pedroren/pekeboard/pekepad-v/cases/top_gasket.stl

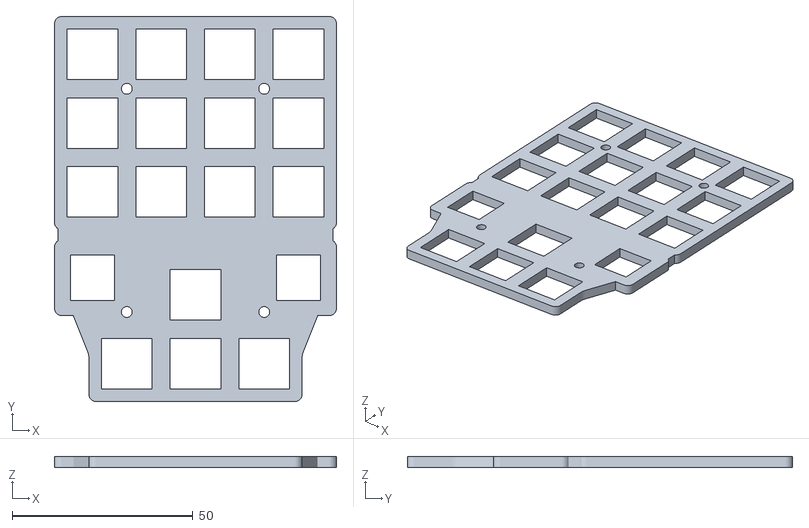
[picture p19: CAD file, 2026-07-04]
pekepad-v/cases/top_gasket.stl
78.0 x 106.5 x 3.00
