pedroren/pekeboard/kicad/3dmodels/SW_SPDT_PCM12.step

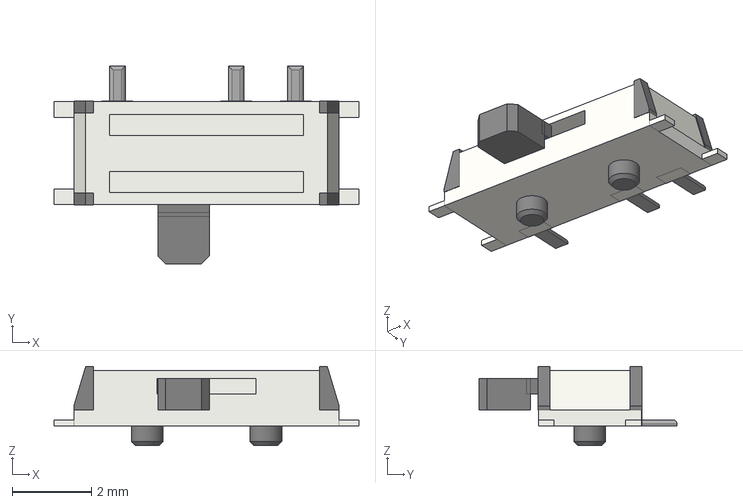
[picture p20: CAD file, 2026-03-06]
kicad/3dmodels/SW_SPDT_PCM12.step
7.70 x 5.00 x 2.00 mm
