pedroren/pekeboard/pekeboard/cases/top_gasket.stl

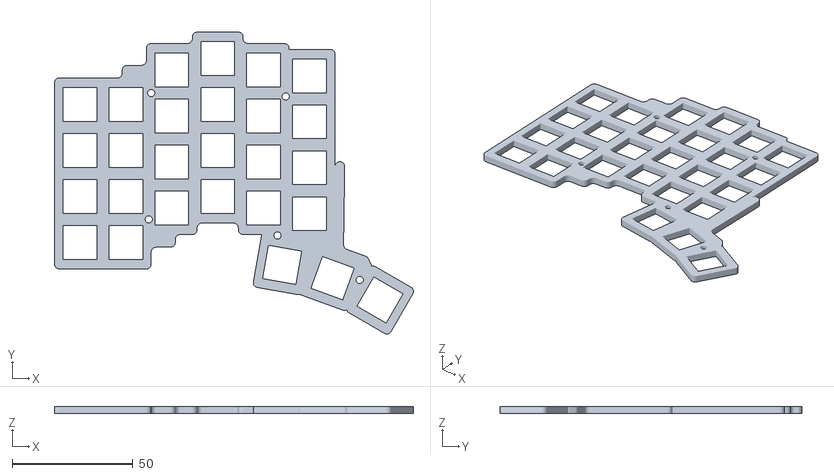
[picture p21: CAD file, 2026-06-26]
pekeboard/cases/top_gasket.stl
148.5 x 124.9 x 3.00
