pedroren/pekeboard/pekepad-v/cases/pcb.stl

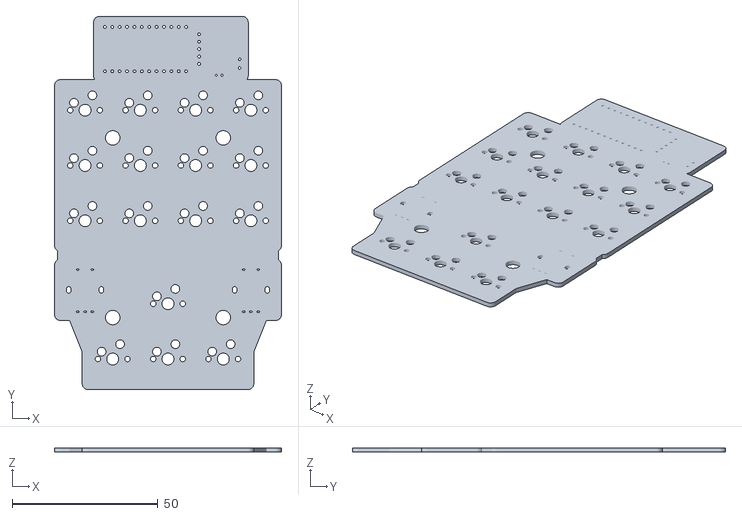
[picture p22: CAD file, 2026-04-15]
pekepad-v/cases/pcb.stl
78.0 x 128.2 x 1.51
