pedroren/pekeboard/pekepad/cases/pekepad_pcb.stl

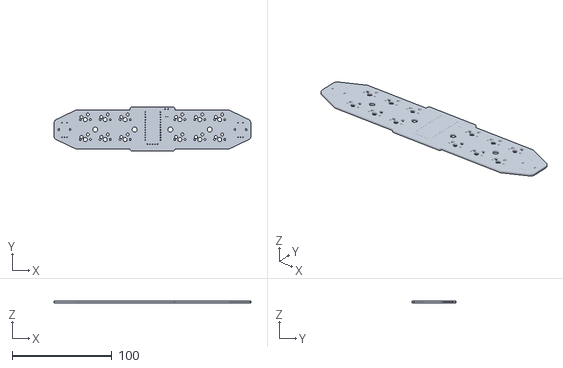
[picture p23: CAD file, 2026-03-21]
pekepad/cases/pekepad_pcb.stl
197.7 x 43.9 x 1.51
