pedroren/pekeboard/kicad/3dmodels/JST_PH_S2B-PH-K_1x02_P2.00mm_Horizontal.step

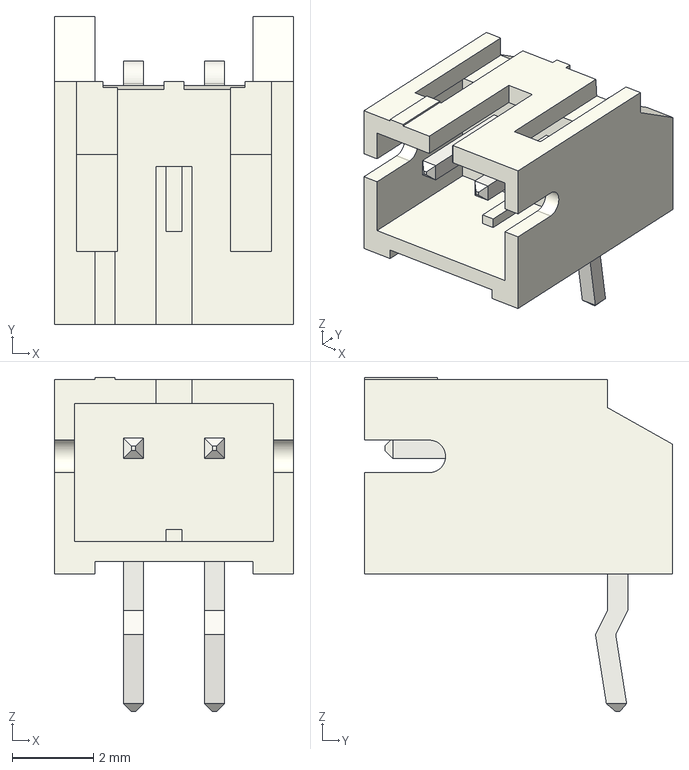
[picture p24: CAD file, 2026-03-06]
kicad/3dmodels/JST_PH_S2B-PH-K_1x02_P2.00mm_Horizontal.step
5.90 x 7.60 x 8.25 mm
