pedroren/pekeboard/pekeboard/cases/switch_plate.stl

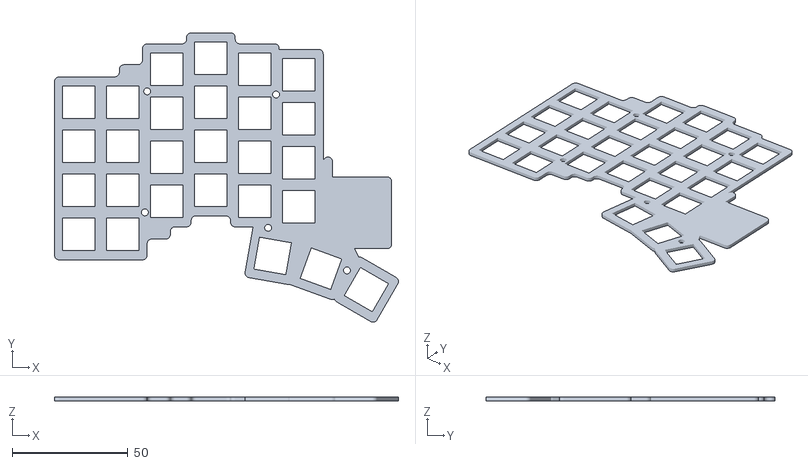
[picture p25: CAD file, 2026-06-26]
pekeboard/cases/switch_plate.stl
148.5 x 124.9 x 1.60
