pedroren/pekeboard/pekepad-v/cases/switch_plate.stl

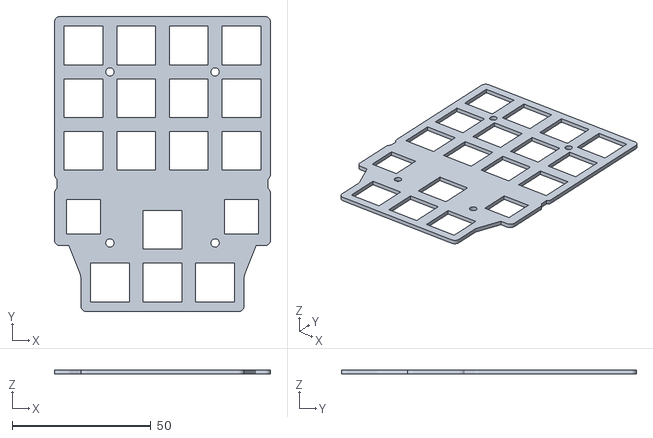
[picture p26: CAD file, 2026-04-15]
pekepad-v/cases/switch_plate.stl
78.0 x 106.5 x 1.60
