pedroren/pekeboard/kicad/3dmodels/D_SOD-123.step

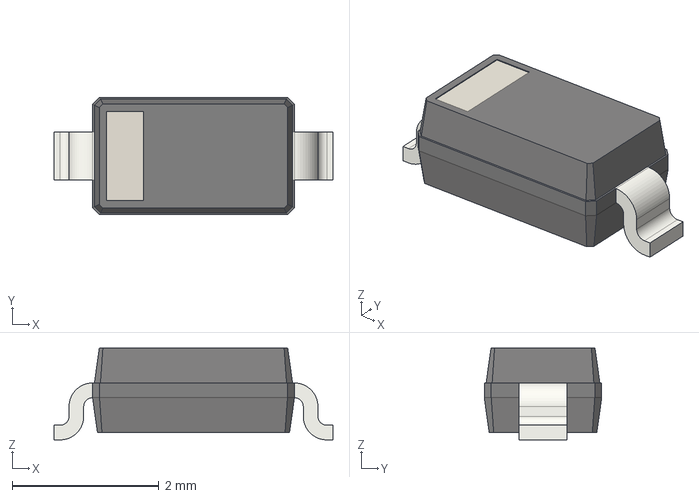
[picture p27: CAD file, 2026-03-06]
kicad/3dmodels/D_SOD-123.step
3.80 x 1.60 x 1.25 mm
