pedroren/pekeboard/pekeboard/cases/pcb_l.stl

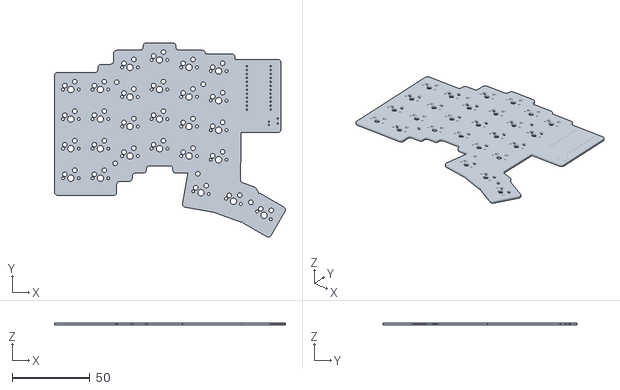
[picture p28: CAD file, 2026-06-18]
pekeboard/cases/pcb_l.stl
148.5 x 124.9 x 1.51
