pedroren/pekeboard/pekeboard/cases/plate_support.stl

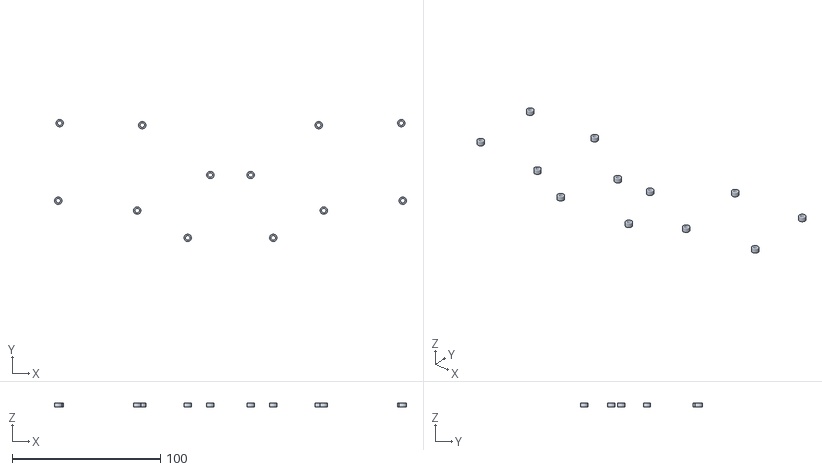
[picture p29: CAD file, 2026-06-07]
pekeboard/cases/plate_support.stl
237.1 x 82.3 x 3.00
