pedroren/pekeboard/pekeboard/cases/pcb.stl

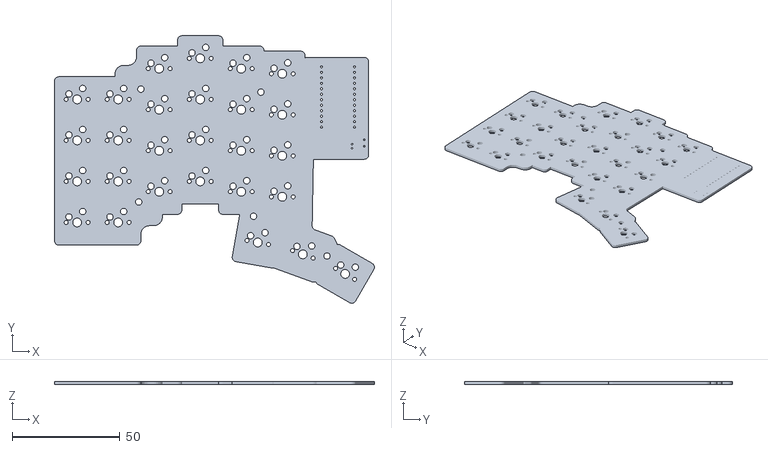
[picture p30: CAD file, 2026-06-07]
pekeboard/cases/pcb.stl
148.2 x 123.9 x 1.51
