pedroren/pekeboard/pekeboard/config.yaml

meta:
  name: pepekey
  version: 1.0
  engine: 4.1.0
  author: pedroren
units:
  kx: u
  ky: u
  p: 0
  # padding for outer keys
  px: 2
  kpx: kx+px
  py: 3
  kpy: ky+py
  # components size
  mcu_y: 34.1
  mcu_x: 18.3
  mcu_d: 3.3+12 # mcu+sockets
  batt_x: 18
  batt_y: 32
  batt_d: 6.5 
  # Defaults to M2 Screws
  screw_size: 1.5
  standoff_size: 2.5
  # Case
  case_d: 1.5
  pcb_d: 1.6
  plate_pcb_gap: 3
  bottom_pcb_gap: 2
  usb_access_x: 13
  usb_access_d: 6
  case_y: case_d+bottom_pcb_gap+pcb_d+plate_pcb_gap+pcb_d
points:
  zones:
    matrix:
      anchor:
        shift: [100, -120] #kicad
      key:
        padding: ky+p
        spread: kx+p
        tags: mx_key
      columns:
        outer:
          key:
            column_net: P008
        pinky:
          key:
            column_net: P022
        ring:
          key:
            stagger: 3u/4
            column_net: P024
        middle:
          key:
            stagger: 1u/4
            column_net: P100
        index:
          key:
            stagger: -1u/4
            column_net: P011
        inner:
          key:
            stagger: -1u/8
            column_net: P106
      rows:
        bottom:
          row_net: P031
        home:
          row_net: P029
        top:
          row_net: P002
        num:
          row_net: P115
    thumbs:
      key:
        padding: ky
        spread: kx+1
        tags: mx_key
      anchor:
        ref:  matrix_inner_bottom
        shift:  [-1u/2,  -1u]
      columns:
        outer:
          key:
            splay: -10
            origin: [-0.7 u, +0.5 u]
            column_net: P011
        middle:
          key:
            splay: -10
            #stagger: -1u/6
            origin: [-0.5 u, -0.5 u]
            #rotate: -6
            column_net: P106
        inner:
          key:
            splay: -10
            #stagger: -1u/4
            #rotate: -6
            origin: [-0.5 u, -0.5 u]
            column_net: P111
      rows:
        thumbrow:
          row_net: P113
    mount_top_left:
      key.tags: [mount]
      anchor:
        - ref: matrix_ring_top
          shift: [-0.5kx +1, 0.5 ky]
    mount_bottom_left:
      key.tags: [mount]
      anchor:
        - ref: matrix_ring_bottom
          shift: [-0.5kx, -0.25ky]
    mount_top_right:
      key.tags: [mount]
      anchor:
        - ref: matrix_inner_top
          shift: [-0.52 kx, .5ky+1]
    mount_palm:
      key.tags: [mount]
      anchor:
        - ref: matrix_index_bottom
          shift: [.3kx, -.6ky]
    mount_thumb:
      key.tags: [mount]
      anchor:
        - ref: thumbs_inner_thumbrow
          shift: [-0.6 kx, 3]
    controller:
      key.tags: [mcu]          
      anchor: 
        - ref: matrix_inner_top
          shift: [.5kx+mcu_x-2, .5ky]
          rotate: 0
    reset_button:
      key.tags: [reset_btn]          
      anchor: 
        - ref: controller
          shift: [.5mcu_x+3, 2]
    power_button:
      key.tags: [power_btn]          
      anchor: 
        - ref: controller
          shift: [.5mcu_x+3, -.75mcu_y+3]          
    case_mount_battery:          
      key.tags: [case_mount]
      anchor:
        - ref: power_button
          shift: [-2, -10]
  mirror:  &mirror
    ref: controller
    distance: 2.5kx        
outlines:
  raw:
    - what: rectangle
      where: [mx_key]
      size: [kx, ky]
      corner: px
    - what: rectangle
      where: [mcu]
      size: [mcu_x, mcu_y]
      corner: px        
    - what: rectangle
      where: [-mx_key,-mcu]
      size: [kx/2, ky/2]
      corner: px      
  keycaps:
    - what: rectangle 
      where: [mx_key]
      size: [kx, ky] 
      corner: 1
  switches:
    - what: rectangle
      where: [mx_key]
      size: 14
  controller:
    - what: rectangle
      where: [mcu]
      size: [mcu_x, mcu_y]
  usb_access:      
    - what: rectangle
      where: [mcu]
      size: [usb_access_x, usb_access_d]
      adjust.shift: [0, .5mcu_y+3]
      corner: 2
  reset_access:
    - what: circle
      where: reset_button
      radius: 2
      adjust.shift: [1.5, 0]
  power_access:      
    - what: rectangle
      where: power_button
      size: [pcb_d+1, usb_access_x-2]
      adjust.shift: [case_d, 0]    
  controller_area:
    - what: rectangle
      where: [mcu]        
      size: [1.5mcu_x+3, 1.5mcu_y-4]
      corner: px
      adjust.shift: [-1,-.25mcu_y+2]
  controller_cover:
     - what: outline
       name: controller_area
       operation: add
     - what: rectangle      
       size: [1.5mcu_x+3, 10]
       corner: px
       where: [mcu]        
       adjust.shift: [-1, -mcu_y]
  battery_area: #Batt/Cable cover
    - what: rectangle
      where: [mcu]
      size: [1.5mcu_x+5, batt_y-1] 
      adjust.shift: [-2, -.5mcu_y-.5batt_y-17]
      corner: px
    - what: rectangle  #Remove right side
      where: mirror_controller            
      size: [200, 200]        
      adjust:
        shift: [-80, 0]
      operation: subtract    
  screw_holes:
    - what: circle
      radius: screw_size    
      where: [mount, case_mount]
  mounting_holes:
    - what: circle
      radius: standoff_size    
      where: [mount, case_mount]
  mounting_holes_left:
    - what: circle
      radius: standoff_size    
      where: [mount, case_mount]    
    - what: rectangle  #Remove right side
      where: mirror_controller            
      size: [200, 200]        
      adjust:
        shift: [-80, 0]
      operation: subtract  
  pcb_support:
    - what: outline
      name: screw_holes
      expand: 1
    - what: rectangle  #Remove right side
      where: mirror_controller            
      size: [200, 200]        
      adjust:
        shift: [-80, 0]
      operation: subtract    
  keywell:
    - what: rectangle 
      where: [mx_key]
      size: [kpx, kpy] 
      corner: 2
      fillet: 2
      bound: true
  thumbs_patch:
    - what: polygon
      operation: stack
      fillet: 2
      points:
        - ref:  thumbs_outer_thumbrow
          shift: [-0.5kpx, -0.5kpy]
        - ref:  thumbs_middle_thumbrow
          shift: [-0.5kpx, -0.5kpy]
        - ref:  thumbs_inner_thumbrow
          shift: [-0.5kpx, -0.5kpy]
        - ref:  thumbs_inner_thumbrow
          shift: [0kpx, 0kpy]          
        - ref:  thumbs_inner_thumbrow
          shift: [-0.5kpx, 0.5kpy]
        - ref:  thumbs_middle_thumbrow
          shift: [0.5kpx, 0.6kpy]
        - ref:  thumbs_middle_thumbrow
          shift: [0kpx, 0.6kpy]
        - ref:  matrix_inner_home # Easier routing
          shift: [.70kpx, 0.6kpy]
        - ref:  thumbs_outer_thumbrow
          shift: [0.5kpx, 0.85kpy]          
        - ref:  thumbs_outer_thumbrow
          shift: [-0.5kpx, 0.75kpy]          
  thumbs_patch_r:
    - what: polygon
      operation: stack
      fillet: 2
      points:
        - ref:  mirror_thumbs_outer_thumbrow
          shift: [-0.5kpx, -0.5kpy]
        - ref:  mirror_thumbs_middle_thumbrow
          shift: [-0.5kpx, -0.5kpy]
        - ref:  mirror_thumbs_inner_thumbrow
          shift: [-0.5kpx, -0.5kpy]
        - ref:  mirror_thumbs_inner_thumbrow
          shift: [0kpx, 0kpy]          
        - ref:  mirror_thumbs_inner_thumbrow
          shift: [-0.5kpx, 0.5kpy]
        - ref:  mirror_thumbs_middle_thumbrow
          shift: [0.5kpx, 0.6kpy]
        - ref: mirror_thumbs_middle_thumbrow
          shift: [0kpx, 0.6kpy]
        - ref: mirror_matrix_inner_home # Easier routing
          shift: [.70kpx, 0.6kpy]
        - ref:  mirror_thumbs_outer_thumbrow
          shift: [0.5kpx, 0.85kpy]          
        - ref:  mirror_thumbs_outer_thumbrow
          shift: [-0.5kpx, 0.75kpy]                    
  base_outline:
    - keywell
    - name: thumbs_patch
      operation: add
      joints: beveled
      fillet: 2
      bound: true
    - name: thumbs_patch_r
      operation: add
      joints: beveled
      fillet: 2
      bound: true
    - controller_area
  bottom_outline:
    - base_outline
    - name: battery_area
      operation: add
      joints: beveled
      fillet: 2
    - -screw_holes
    - what: rectangle  #Remove right side
      where: mirror_controller            
      size: [200, 200]        
      adjust:
        shift: [-80, 0]
      operation: subtract
  outer_area:
    - what: outline
      name: bottom_outline
      expand: case_d+1
      joints: beveled
    - what: rectangle  #Remove right side
      where: mirror_controller            
      size: [200, 200]        
      adjust:
        shift: [-80, 0]
      operation: subtract
  plate:
    - keywell
    - thumbs_patch
    - thumbs_patch_r
    - "-switches"
    - "-screw_holes"
    - what: rectangle  #Remove right side
      where: mirror_controller            
      size: [200, 200]        
      adjust:
        shift: [-80, 0]
      operation: subtract
  pcb:
    - base_outline
    - "-screw_holes"     
  pcb_left:
    - what: outline
      name: pcb
      operation: add        
    - what: rectangle  #Remove right side
      where: mirror_controller            
      size: [200, 200]        
      adjust:
        shift: [-80, 0]
      operation: subtract
  pcb_right:
    - what: outline
      name: pcb
    - what: rectangle #Remove left side
      where: '/^controller/'
      size: [200, 200]        
      adjust:
        shift: [-80, 0]
      operation: subtract
  # For verification
  switches_screws: 
    - base_outline
    - -switches
    - -mounting_holes
  pcb_switches: 
    - pcb
    - -switches
  pcb_keycaps: 
    - pcb
    - -keycaps
pcbs:
  top_plate:
    template: kicad8
    outlines:
      edge:
        outline: plate
        layer: Edge.Cuts
  bottom_plate:
    template: kicad8
    outlines:
      edge:
        outline: bottom_outline
        layer: Edge.Cuts        
  pepekey_l:
    template: kicad8
    outlines:
      main:
        outline: pcb_left
        layer: Edge.Cuts
        asym: source 
    footprints:
      # gnd_fillzone:
      #   what: ceoloide/utility_filled_zone
      #   where:
      #     ref.aggregate.parts: [matrix_outer_top]
      mounting_holes:
        what: ceoloide/mounting_hole_npth
        where:  '/^mount_/'
      mx_hotswap:
        what: ceoloide/switch_mx
        where: '/^(matrix|thumbs)_/'
          #- /matrix_.*/
          #- /thumbs_.*/          
        params:
          include_keycap: true
          reversible: false
          hotswap: true
          from: "{{column_net}}"
          to: "{{colrow}}"
          switch_3dmodel_filename: '${KIPRJMOD}/../../kicad/3dmodels/SW_Hotswap_Kailh_MX.stp'
          switch_3dmodel_xyz_rotation: [0,180,180]
          switch_3dmodel_xyz_offset: [0, 0, -1.9]
      diode:
        what: ceoloide/diode_tht_sod123
        where: '/^(matrix|thumbs)_/'
          #- /matrix_.*/
          #- /thumbs_.*/
        adjust.shift: [0, -5]
        params:
          reversible: false
          side: B
          from: "{{colrow}}"
          to: "{{row_net}}"
          diode_3dmodel_filename: '${KIPRJMOD}/../../kicad/3dmodels/D_SOD-123.step'
      mcu:
        what: ceoloide/mcu_nice_nano
        where: '/^controller/'#mcu
        params:
          #side: F
          reversible: false
          show_via_labels: false
          P21_label: "031"
          P20_label: "029"
          P19_label: "002"
          P18_label: "115"
          P15_label: "113"
          P14_label: "111"
          P16_label: "010"
          P10_label: "009"
          P1_label: "006"
          P0_label: "008"
          P2_label: "017"
          P3_label: "020"
          P4_label: "022"
          P5_label: "024"
          P6_label: "100"
          P7_label: "011"
          P8_label: "104"
          P9_label: "106"
          P21: P031
          P20: P029
          P19: P002
          P18: P115
          P15: P113
          P14: P111
          P16: P010
          P10: P009
          P1: P006
          P0: P008
          P2: P017
          P3: P020
          P4: P022
          P5: P024
          P6: P100
          P7: P011
          P8: P104
          P9: P106
      reset_switch:
        what: ceoloide/reset_switch_smd_side
        where: '/^reset_button/'#[reset_btn]
        adjust:
          shift: [0, 0]
          rotate: 270
        params:
          reversible: false          
          from: GND
          to: RST
          reset_switch_3dmodel_filename: '${KIPRJMOD}/../../kicad/3dmodels/Panasonic_EVQPUJ_EVQPUA.step'
          reset_switch_3dmodel_xyz_rotation: [0,0,0]
      power_switch:
        what: ceoloide/power_switch_smd_side
        params:
          reversible: false
          side: F
          switch_3dmodel_filename: '${KIPRJMOD}/../../kicad/3dmodels/SW_SPDT_PCM12.step'
          switch_3dmodel_xyz_rotation: [0,0,-90]
        where:  '/^power_button/'#[power_btn]
        adjust:
          shift: [0, 0]
          rotate: 0
      batt_connector:
        what: ceoloide/battery_connector_jst_ph_2
        params:
          reversible: false
          side: F
          battery_connector_3dmodel_filename: '${KIPRJMOD}/../../kicad/3dmodels/JST_PH_S2B-PH-K_1x02_P2.00mm_Horizontal.step'
          battery_connector_3dmodel_xyz_rotation: [0,0,0]
          battery_connector_3dmodel_xyz_offset: [-1, 0, 0]
        where:  '/^controller/'#[mcu]
        adjust:
          shift: [.5kx-3, -.5mcu_y-7]
          rotate: -90
      pcb_label:
        what: ceoloide/utility_text
        params:
          text: 'Pekeboard v1.0 by pedroren'    
        where:  '/^matrix_inner_bottom/'
        adjust:
          shift: [1/2kx+2,0]
          rotate: -90    
  pepekey_r:
    template: kicad8
    outlines:
      main:
        outline: pcb_right
        layer: Edge.Cuts
        asym: source 
    footprints:
      # gnd_fillzone:
      #   what: ceoloide/utility_filled_zone
      #   where:
      #     ref.aggregate.parts: [matrix_outer_top]
      mounting_holes:
        what: ceoloide/mounting_hole_npth
        where:  '/^mirror_mount_/'
      mx_hotswap:
        what: ceoloide/switch_mx
        where: '/^(mirror_matrix|mirror_thumbs)_/'
          #- /matrix_.*/
          #- /thumbs_.*/          
        params:
          include_keycap: true
          reversible: false
          hotswap: true
          from: "{{column_net}}"
          to: "{{colrow}}"
          switch_3dmodel_filename: '${KIPRJMOD}/../../kicad/3dmodels/SW_Hotswap_Kailh_MX.stp'
          switch_3dmodel_xyz_rotation: [0,180,180]
          switch_3dmodel_xyz_offset: [0, 0, -1.9]
      diode:
        what: ceoloide/diode_tht_sod123
        where: '/^(mirror_matrix|mirror_thumbs)_/'
          #- /matrix_.*/
          #- /thumbs_.*/
        adjust.shift: [0, -5]
        params:
          reversible: false
          side: B
          from: "{{colrow}}"
          to: "{{row_net}}"
          diode_3dmodel_filename: '${KIPRJMOD}/../../kicad/3dmodels/D_SOD-123.step'
      mcu:
        what: ceoloide/mcu_nice_nano
        where: '/^mirror_controller/'#mcu
        params:
          #side: F
          reversible: false
          show_via_labels: false
          P21_label: "031"
          P20_label: "029"
          P19_label: "002"
          P18_label: "115"
          P15_label: "113"
          P14_label: "111"
          P16_label: "010"
          P10_label: "009"
          P1_label: "006"
          P0_label: "008"
          P2_label: "017"
          P3_label: "020"
          P4_label: "022"
          P5_label: "024"
          P6_label: "100"
          P7_label: "011"
          P8_label: "104"
          P9_label: "106"
          P21: P031
          P20: P029
          P19: P002
          P18: P115
          P15: P113
          P14: P111
          P16: P010
          P10: P009
          P1: P006
          P0: P008
          P2: P017
          P3: P020
          P4: P022
          P5: P024
          P6: P100
          P7: P011
          P8: P104
          P9: P106
      reset_switch:
        what: ceoloide/reset_switch_smd_side
        where: '/^mirror_reset_button/'#[reset_btn]
        adjust:
          shift: [0, 0]
          rotate: 270
        params:
          reversible: false          
          from: GND
          to: RST
          reset_switch_3dmodel_filename: '${KIPRJMOD}/../../kicad/3dmodels/Panasonic_EVQPUJ_EVQPUA.step'
          reset_switch_3dmodel_xyz_rotation: [0,0,0]
      power_switch:
        what: ceoloide/power_switch_smd_side
        params:
          reversible: false
          side: F
          switch_3dmodel_filename: '${KIPRJMOD}/../../kicad/3dmodels/SW_SPDT_PCM12.step'
          switch_3dmodel_xyz_rotation: [0,0,-90]
        where:  '/^mirror_power_button/'#[power_btn]
        adjust:
          shift: [0, 0]
          rotate: 180
      batt_connector:
        what: ceoloide/battery_connector_jst_ph_2
        params:
          reversible: false
          side: F
          battery_connector_3dmodel_filename: '${KIPRJMOD}/../../kicad/3dmodels/JST_PH_S2B-PH-K_1x02_P2.00mm_Horizontal.step'
          battery_connector_3dmodel_xyz_rotation: [0,0,0]
          battery_connector_3dmodel_xyz_offset: [-1, 0, 0]
        where:  '/^mirror_controller/'#[mcu]
        adjust:
          shift: [.5kx-3, -.5mcu_y-7]
          rotate: -90        
      pcb_label:
        what: ceoloide/utility_text
        params:
          text: 'Pekeboard v1.0 by pedroren'    
        where:  '/^mirror_matrix_inner_bottom/'
        adjust:
          shift: [1/2kx+2,0]
          rotate: -90
  pepekey_dual: #reversible version
    template: kicad8
    outlines:
      main:
        outline: pcb_left
        layer: Edge.Cuts
        asym: source 
    footprints:
      # gnd_fillzone:
      #   what: ceoloide/utility_filled_zone
      #   where:
      #     ref.aggregate.parts: [matrix_outer_top]
      mounting_holes:
        what: ceoloide/mounting_hole_npth
        where:  '/^mount_/'
      mx_hotswap:
        what: ceoloide/switch_mx
        where: '/^(matrix|thumbs)_/'
          #- /matrix_.*/
          #- /thumbs_.*/          
        params:
          include_keycap: true
          reversible: true
          hotswap: true
          from: "{{column_net}}"
          to: "{{colrow}}"
          switch_3dmodel_filename: '${KIPRJMOD}/../../kicad/3dmodels/SW_Hotswap_Kailh_MX.stp'
          switch_3dmodel_xyz_rotation: [0,180,180]
          switch_3dmodel_xyz_offset: [0, 0, -1.9]
      diode:
        what: ceoloide/diode_tht_sod123
        where: '/^(matrix|thumbs)_/'
          #- /matrix_.*/
          #- /thumbs_.*/
        adjust.shift: [0, -5]
        params:
          reversible: true
          side: B
          from: "{{colrow}}"
          to: "{{row_net}}"
          diode_3dmodel_filename: '${KIPRJMOD}/../../kicad/3dmodels/D_SOD-123.step'
      mcu:
        what: ceoloide/mcu_nice_nano
        where: '/^controller/'#mcu
        params:
          #side: F
          reversible: true
          show_via_labels: false
          P21_label: "031"
          P20_label: "029"
          P19_label: "002"
          P18_label: "115"
          P15_label: "113"
          P14_label: "111"
          P16_label: "010"
          P10_label: "009"
          P1_label: "006"
          P0_label: "008"
          P2_label: "017"
          P3_label: "020"
          P4_label: "022"
          P5_label: "024"
          P6_label: "100"
          P7_label: "011"
          P8_label: "104"
          P9_label: "106"
          P21: P031
          P20: P029
          P19: P002
          P18: P115
          P15: P113
          P14: P111
          P16: P010
          P10: P009
          P1: P006
          P0: P008
          P2: P017
          P3: P020
          P4: P022
          P5: P024
          P6: P100
          P7: P011
          P8: P104
          P9: P106
      reset_switch:
        what: ceoloide/reset_switch_smd_side
        where: '/^reset_button/'#[reset_btn]
        adjust:
          shift: [0, 0]
          rotate: 270
        params:
          reversible: true          
          from: GND
          to: RST
          reset_switch_3dmodel_filename: '${KIPRJMOD}/../../kicad/3dmodels/Panasonic_EVQPUJ_EVQPUA.step'
          reset_switch_3dmodel_xyz_rotation: [0,0,0]
      power_switch:
        what: ceoloide/power_switch_smd_side
        params:
          reversible: true
          side: F
          switch_3dmodel_filename: '${KIPRJMOD}/../../kicad/3dmodels/SW_SPDT_PCM12.step'
          switch_3dmodel_xyz_rotation: [0,0,-90]
        where:  '/^power_button/'#[power_btn]
        adjust:
          shift: [0, 0]
          rotate: 0
      batt_connector:
        what: ceoloide/battery_connector_jst_ph_2
        params:
          reversible: true
          side: F
          battery_connector_3dmodel_filename: '${KIPRJMOD}/../../kicad/3dmodels/JST_PH_S2B-PH-K_1x02_P2.00mm_Horizontal.step'
          battery_connector_3dmodel_xyz_rotation: [0,0,0]
          battery_connector_3dmodel_xyz_offset: [-1, 0, 0]
        where:  '/^controller/'#[mcu]
        adjust:
          shift: [.5kx-3, -.5mcu_y-7]
          rotate: -90
      pcb_label:
        what: ceoloide/utility_text
        params:
          text: 'Pekeboard v1.0 by pedroren'    
        where:  '/^matrix_inner_bottom/'
        adjust:
          shift: [1/2kx+2,0]
          rotate: -90    
cases:
  _pcb:
    - name: pcb_left
      extrude: pcb_d
      shift: [0,0,case_d+pcb_d+bottom_pcb_gap]
  _switch_plate:
      - name: plate
        extrude: pcb_d
        shift: [0, 0, case_y-pcb_d]
  _standoffs:
    - name: mounting_holes_left
      extrude: case_d+bottom_pcb_gap+pcb_d
  _pcb_support:
    - name: pcb_support
      extrude: pcb_d+bottom_pcb_gap
  _holes:
    - name: screw_holes
      extrude: case_y+case_y
  _usb_cutout:
    - name: usb_access
      extrude: case_d+2
      shift: [0, 0, case_d+pcb_d+bottom_pcb_gap+1]
      rotate: [90,0,0]
  _reset_cutout:
    - name: reset_access
      extrude: case_d+2
      shift: [0, 0, case_d+2pcb_d+bottom_pcb_gap]
      rotate: [0,90,0]
  _power_cutout:
    - name: power_access
      extrude: case_d+2
      shift: [0, 0, case_d+2pcb_d+bottom_pcb_gap]     
      rotate: [0,90,0]
  _battery_cover:
    - name: battery_area
      extrude: pcb_d
      shift: [0, 0, case_y-pcb_d]
  pcb:
    - _pcb      
  switch_plate:
    - _switch_plate      
    - _battery_cover
    - -_holes
  _bottom:
    - name: outer_area
      extrude: pcb_d
  _outer_block:
    - name: outer_area
      extrude: case_y
  _inner_block:
    - what: outline
      name: bottom_outline
      shift: [0, 0, case_d]
      extrude: case_y-case_d
    - what: case
      name: _standoffs
      operation: subtract
  _precase:
    - _outer_block
    - -_inner_block
  case:
    - _precase
    - _bottom
    - _pcb_support
    - _standoffs
    - -_holes
    - -_usb_cutout
    - -_reset_cutout
    - -_power_cutout
  sandwich_case:
    - name: pcb_left
      extrude: pcb_d
      operation: add
    - name: battery_area
      extrude: pcb_d 
      operation: add
    - _pcb_support
    - _standoffs
    - -_holes
  plate_support:
    - what: outline
      name: mounting_holes
      extrude: plate_pcb_gap
    - what: outline
      name: screw_holes
      extrude: plate_pcb_gap
      operation: subtract
  top_gasket:
      - name: plate
        extrude: plate_pcb_gap
        shift: [0, 0, 0]    
  controller_cover:
      - name: controller_cover
        extrude: pcb_d
        shift: [0, 0, case_y]    
      - -_holes
  case_plate_preview: # Assembly compatibility
    - case
    - switch_plate
  case_pcb_preview: # Assembly compatibility
    - case
    - pcb
  pcb_plate_preview: # Assembly compatibility
    - switch_plate
    - pcb
  sw_case_plate_preview: # Assembly compatibility
    - sandwich_case
    - switch_plate
    - controller_cover
sw_case_pcb_preview: # Assembly compatibility
    - sandwich_case
    - pcb
    
